Milind220/Wireless-Charger/Simulation and Modelling/simulation_picture.png

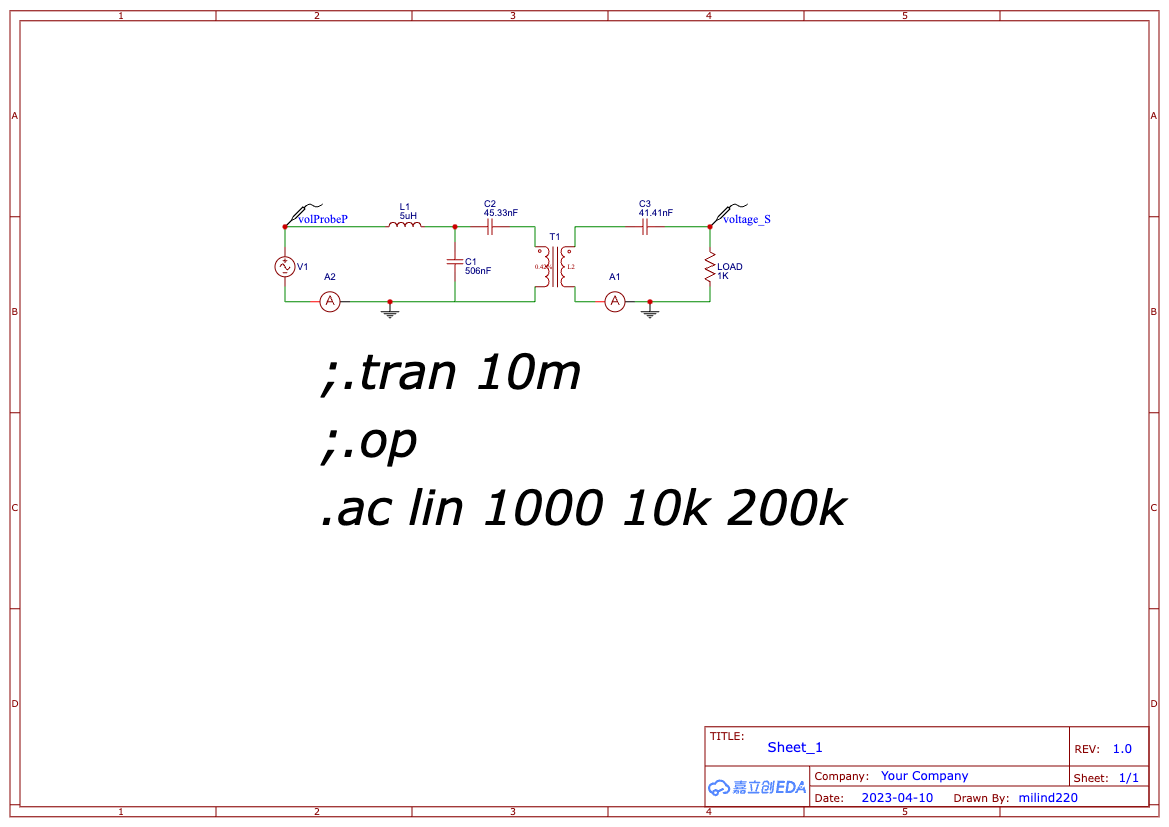
Simulation and Modelling/simulation_picture.png
